noahpettit/surgeryBot/Hardware/Stepper_mount/usbCameraMount2.pdf

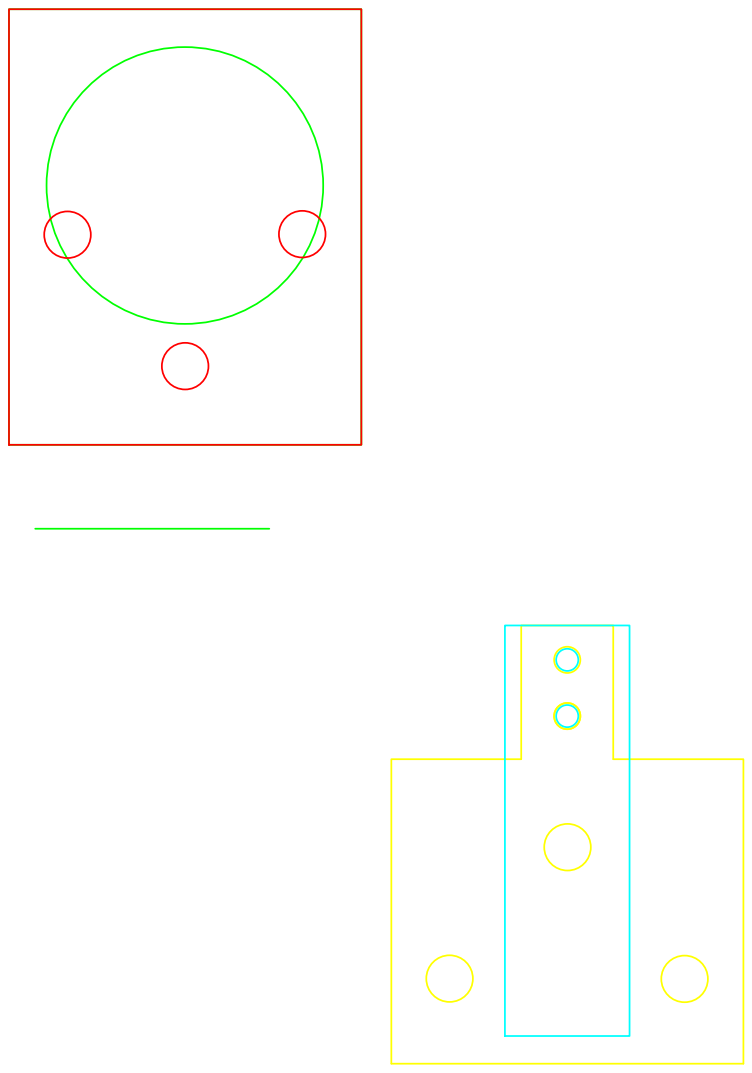
[picture p14: page 1]
