noahpettit/surgeryBot/Hardware/Stepper_mount/usbCameraMount3.pdf

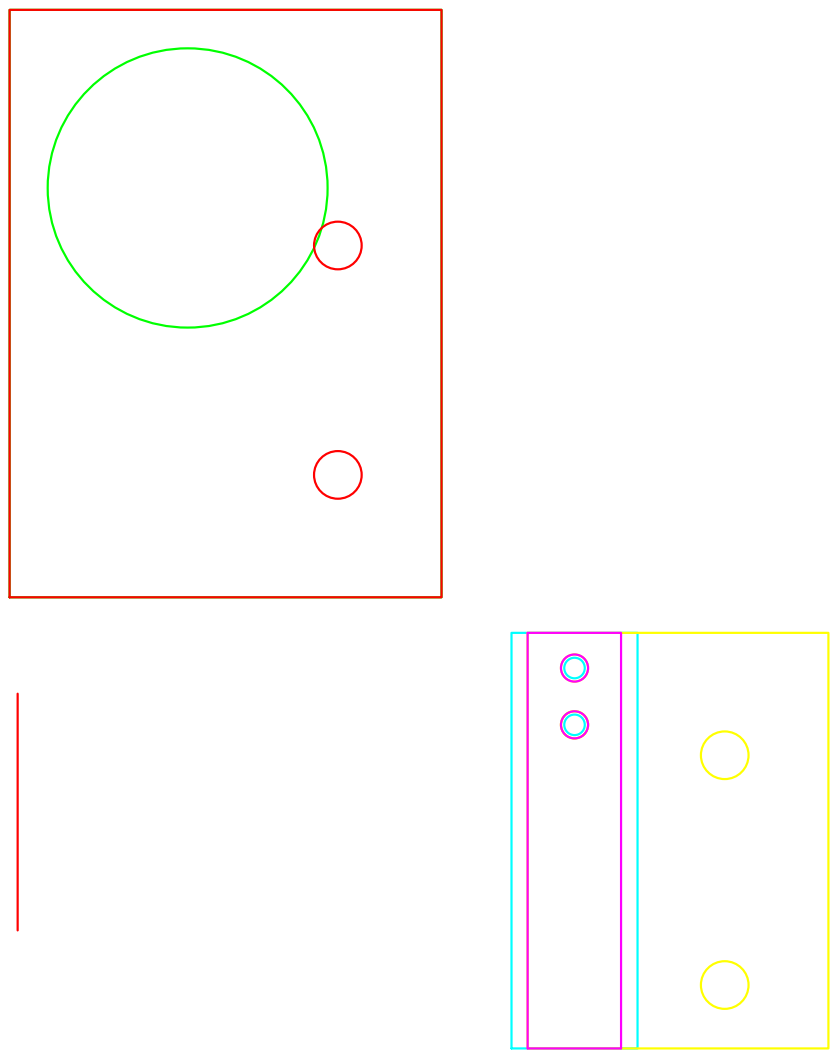
[picture p15: page 1]
