noahpettit/surgeryBot/Hardware/Stepper_mount/StepperMountAndGears_v2.pdf

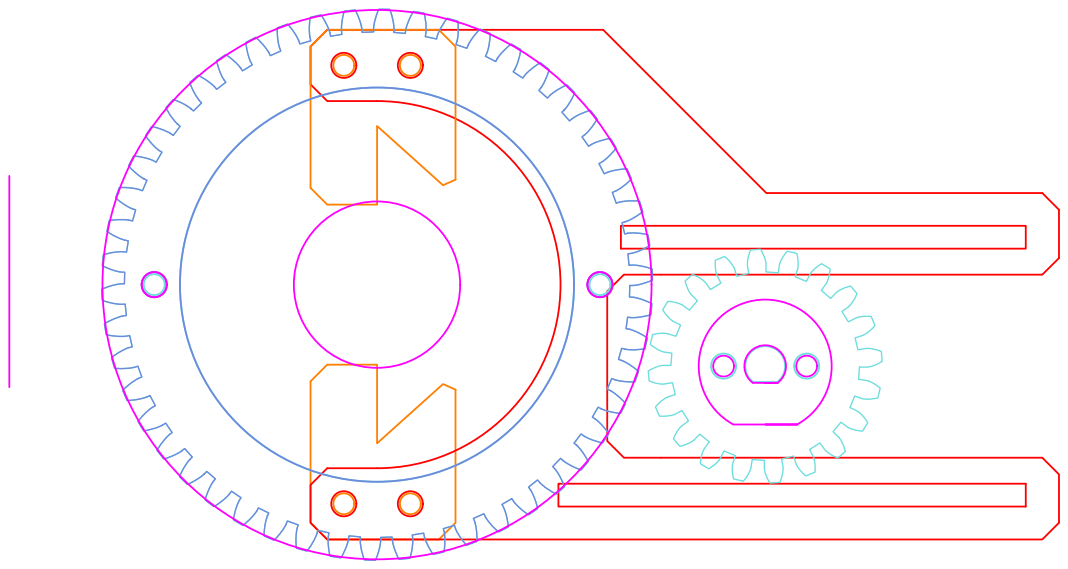
[picture p16: page 1]
